requireiot/BasicSatellite/pictures/1/Basic Satellite 2.jpg

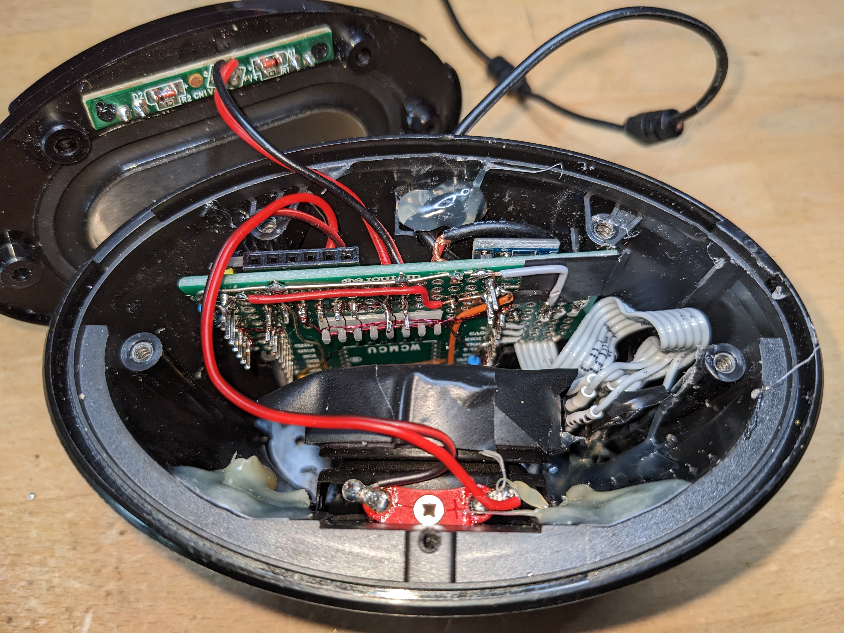
pictures/1/Basic Satellite 2.jpg
