requireiot/BasicSatellite/pictures/1/Basic Satellite 4.jpg

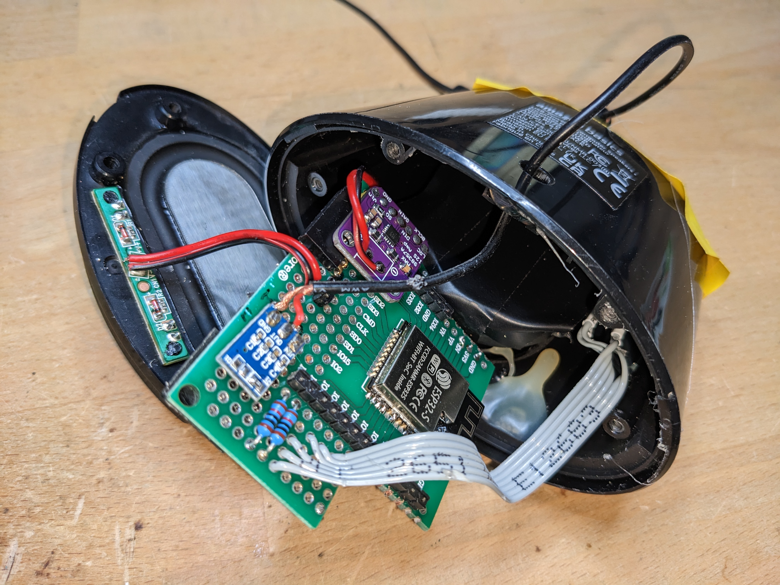
pictures/1/Basic Satellite 4.jpg
