requireiot/BasicSatellite/hardware/Basic-Satellite.kicad_sch

## KiCad design hardware/Basic-Satellite.kicad_sch (2023-10-31)

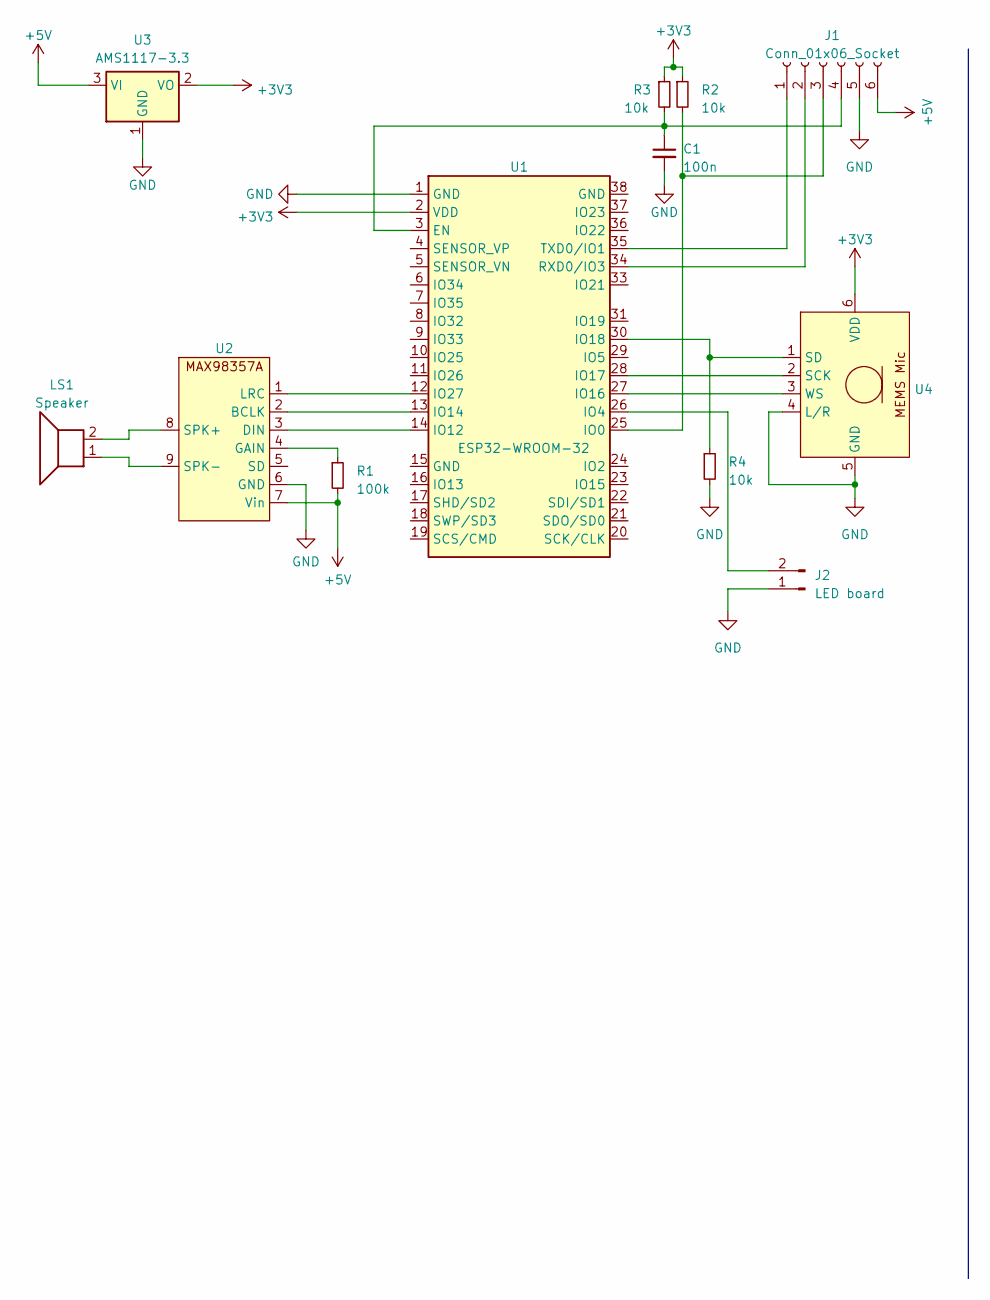
[picture p14: schematic Basic-Satellite.kicad_sch]

Parts:
C1: 100n
J1: Conn_01x06_Socket
J2: LED board
LS1: Speaker
R1: 100k
R2, R3, R4: 10k
U1: ESP32-WROOM-32
U2, U4: (no value)
U3: AMS1117-3.3; SOT-223-3_TabPin2

Connections:
+3V3: R2.1, R3.1, U1.2 (VDD), U3.2 (VO), U4.6 (VDD)
+5V: J1.6, R1.2, U2.7 (Vin), U3.3 (VI)
GND: C1.2, J1.5, J2.1, R4.2, U1.1 (GND), U2.6 (GND), U3.1 (GND), U4.4 (L/R), U4.5 (GND)
unnamed: C1.1, J1.4, R3.2, U1.3 (EN)
unnamed: J1.1, U1.35 (TXD0/IO1)
unnamed: J1.2, U1.34 (RXD0/IO3)
unnamed: J1.3, R2.2, U1.25 (IO0)
unnamed: J2.2, U1.26 (IO4)
unnamed: LS1.1, U2.9 (SPK-)
unnamed: LS1.2, U2.8 (SPK+)
unnamed: R1.1, U2.4 (GAIN)
unnamed: R4.1, U1.30 (IO18), U4.1 (SD)
unnamed: U1.12 (IO27), U2.1 (LRC)
unnamed: U1.13 (IO14), U2.2 (BCLK)
unnamed: U1.14 (IO12), U2.3 (DIN)
unnamed: U1.27 (IO16), U4.3 (WS)
unnamed: U1.28 (IO17), U4.2 (SCK)
